bdring/FluidDial/data/jogbg.png

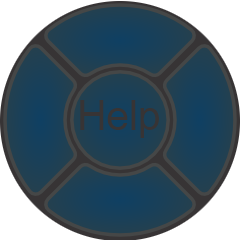
data/jogbg.png
