bdring/FluidDial/docs/images/switchConnectionScene.png

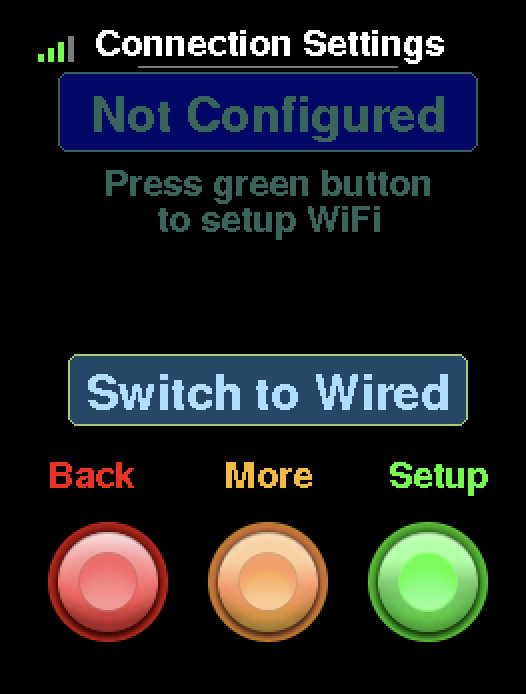
docs/images/switchConnectionScene.png
