bdring/FluidDial/src/Scene.cpp

// Copyright (c) 2023 Mitch Bradley
// Use of this source code is governed by a GPLv3 license that can be found in the LICENSE file.

#include "Scene.h"
#include "ConfigItem.h"
#include "System.h"
#ifdef USE_WIFI
#    include "WiFiConnection.h"
#endif

#ifndef ARDUINO
#    include <sys/stat.h>
#    include <sys/types.h>
#endif
#include <vector>

extern Scene homingScene;
extern Scene statusScene;

Scene* current_scene = nullptr;

int touchX;
int touchY;
int touchDeltaX;
int touchDeltaY;

std::vector<Scene*> scene_stack;

void activate_scene(Scene* scene, void* arg) {
    bool prev_show = !current_scene || current_scene->showButtons();
    if (current_scene) {
        current_scene->onExit();
    }
    current_scene = scene;
    current_scene->onEntry(arg);
    current_scene->reDisplay();
    if (current_scene->showButtons() != prev_show) {
        redrawButtons();
    }
}
void push_scene(Scene* scene, void* arg) {
    scene_stack.push_back(current_scene);
    activate_scene(scene, arg);
}
void pop_scene(void* arg) {
    if (scene_stack.size()) {
        Scene* last_scene = scene_stack.back();
        scene_stack.pop_back();
        activate_scene(last_scene, arg);
    }
}
void activate_at_top_level(Scene* scene, void* arg) {
    scene_stack.clear();
    activate_scene(scene, arg);
}
Scene* parent_scene() {
    return scene_stack.size() ? scene_stack.back() : nullptr;
}

bool touchIsCenter() {
    // Convert from screen coordinates to 0,0 in the center
    Point ctr = Point { touchX, touchY }.from_display();

    int center_radius = display_short_side() / 6;

    return (ctr.x * ctr.x + ctr.y * ctr.y) < (center_radius * center_radius);
}

void dispatch_button(bool pressed, int button) {
    switch (button) {
        case 0:
            if (pressed) {
                current_scene->onRedButtonPress();
            } else {
                current_scene->onRedButtonRelease();
            }
            break;
        case 1:
            if (pressed) {
                current_scene->onDialButtonPress();
            } else {
                current_scene->onDialButtonRelease();
            }
            break;
        case 2:
            if (pressed) {
                current_scene->onGreenButtonPress();
            } else {
                current_scene->onGreenButtonRelease();
            }
            break;
        default:
            break;
    }
}
void dispatch_touch() {
    static m5::touch_state_t last_touch_state = {};

    auto t = touch.getDetail();
    if (t.state != last_touch_state) {
        last_touch_state = t.state;
        touchX           = t.x - sprite_offset.x;
        touchY           = t.y - sprite_offset.y;
        int delta;
        if (screen_encoder(t.x, t.y, delta) && t.state == m5::touch_state_t::touch) {
            current_scene->onEncoder(delta);
            return;
        }
        int button;
       
        if (screen_button_touched(t.state == m5::touch_state_t::touch, t.x, t.y, button)) {
            if (t.state == m5::touch_state_t::touch) {
                dispatch_button(true, button);
            } else if (t.state == m5::touch_state_t::none) {
                dispatch_button(false, button);
            }
            return;
        }
        if (touchX < 0) {
            return;
        }
        if (t.state == m5::touch_state_t::touch) {
            current_scene->onTouchPress();
        } else if (t.state == m5::touch_state_t::none) {
            current_scene->onTouchRelease();
        }
        if (t.wasClicked()) {
            current_scene->onTouchClick();
        } else if (t.wasHold()) {
            current_scene->onTouchHold();
        } else if (t.state == m5::touch_state_t::flick_end) {
            touchDeltaX = t.distanceX();
            touchDeltaY = t.distanceY();

            int absX = abs(touchDeltaX);
            int absY = abs(touchDeltaY);
            if (absY > 60 && absX < (absY * 2)) {
                if (touchDeltaY > 0) {
                    current_scene->onDownFlick();
                } else {
                    current_scene->onUpFlick();
                }
            } else if (absX > 60 && absY < (absX * 2)) {
                if (touchDeltaX > 0) {
                    current_scene->onRightFlick();
                } else {
                    current_scene->onLeftFlick();
                }
            } else {
                current_scene->onTouchFlick();
            }
        }
    }
}

ActionHandler action = nullptr;

void schedule_action(ActionHandler _action) {
    action = _action;
}

// Coalesced redraw bookkeeping. See Scene.h for rationale.
static volatile bool s_redisplay_dirty   = false;
static uint32_t      s_last_redisplay_ms = 0;

void request_redisplay() {
    s_redisplay_dirty = true;
}

void service_redisplay() {
    if (!s_redisplay_dirty) {
        return;
    }
    uint32_t now = millis();
    // Cap UI refresh to UPDATE_RATE_MS (~30 ms). Multiple parser callbacks
    // in the same window collapse to one reDisplay.
    if ((int32_t)(now - s_last_redisplay_ms) < (int32_t)UPDATE_RATE_MS) {
        return;
    }
    s_redisplay_dirty   = false;
    s_last_redisplay_ms = now;
    if (current_scene) {
        current_scene->reDisplay();
    }
}

void dispatch_events() {
    update_events();
    service_config_requests();

    static int16_t oldEncoder   = 0;
    int16_t        newEncoder   = get_encoder();
    int16_t        encoderDelta = newEncoder - oldEncoder;
    if (encoderDelta) {
        oldEncoder = newEncoder;

        int16_t scaledDelta = current_scene->scale_encoder(encoderDelta);
        if (scaledDelta && !ui_locked()) {
            current_scene->onEncoder(scaledDelta);
        }
    }

    if (!ui_locked()) {
        bool pressed;
        int  button;
        if (switch_button_touched(pressed, button)) {
            dispatch_button(pressed, button);
        }

        dispatch_touch();
    }

    current_scene->onPoll();

    if (!fnc_is_connected()) {
        if (state != Disconnected) {
            set_disconnected_state();
#ifdef USE_WIFI
            wifi_force_ws_reconnect();
#endif
            extern Scene menuScene;
            activate_at_top_level(&menuScene);
            fnc_realtime(StatusReport);
        }
    }
    if (action) {
        action();
        action = nullptr;
    }
}

static const char* setting_name(const char* base_name, int axis) {
    static char name[32];
    if (axis == -1) {
        return base_name;
    }
    sprintf(name, "%s%c", base_name, axisNumToChar(axis));
    return name;
}

void Scene::setPref(const char* name, int value) {
    setPref(name, -1, value);
}
void Scene::getPref(const char* name, int* value) {
    getPref(name, -1, value);
}

void Scene::setPref(const char* base_name, int axis, int value) {
    if (!_prefs) {
        return;
    }
    nvs_set_i32(_prefs, setting_name(base_name, axis), value);
}
void Scene::getPref(const char* base_name, int axis, int* value) {
    if (!_prefs) {
        return;
    }
    nvs_get_i32(_prefs, setting_name(base_name, axis), reinterpret_cast<int32_t*>(value));
}
void Scene::setPref(const char* base_name, int axis, const char* value) {
    if (!_prefs) {
        return;
    }
    nvs_set_str(_prefs, setting_name(base_name, axis), value);
}
void Scene::getPref(const char* base_name, int axis, char* value, int maxlen) {
    if (!_prefs) {
        return;
    }
    size_t len = maxlen;
    nvs_get_str(_prefs, setting_name(base_name, axis), value, &len);
}
bool Scene::initPrefs() {
    if (_prefs) {
        return false;  // Already open
    }
    _prefs = nvs_init(name());
    return _prefs;
}

int Scene::scale_encoder(int delta) {
    _encoder_accum += delta;
    int res = _encoder_accum / _encoder_scale;
    _encoder_accum %= _encoder_scale;
    return res;
}

void Scene::background() {
    system_background();
}

void act_on_state_change() {
    current_scene->onStateChange(previous_state);
}
