bdring/FluidDial/src/SystemMacOS.cpp

// 2026 - Figamore
// Use of this source code is governed by a GPLv3 license that can be found in the LICENSE file.

// System interface routines for macOS (native SDL preview build)

#include "stdio.h"

#include "System.h"
#include "FluidNCModel.h"
#include "M5GFX.h"
#include "Drawing.h"
#include "NVS.h"
#ifdef USE_WIFI
#    include "WiFiConnection.h"
#    include "PeerLink.h"
#endif

#include <fcntl.h>
#include <termios.h>
#include <unistd.h>
#include <sys/stat.h>
#include <string.h>
#include <stdlib.h>

LGFX_Device& display = M5.Display;
LGFX_Sprite  canvas(&M5.Display);

m5::Speaker_Class& speaker = M5.Speaker;
m5::Touch_Class&   touch   = M5.Touch;

bool round_display = true;

void system_background() {
    drawPngFile("PCBackground.png", 0, 0);
}

void update_events() {
    lgfx::Panel_sdl::loop();
    M5.update();
}

extern "C" int milliseconds() {
    return m5gfx::millis();
}

void delay_ms(uint32_t ms) {
    SDL_Delay(ms);
}

void drawPngFile(const char* filename, int x, int y) {
    drawPngFile(&canvas, filename, x, y);
}
void drawPngFile(LGFX_Sprite* sprite, const char* filename, int x, int y) {
    std::string fn("data/");
    fn += filename;
    sprite->drawPngFile(fn.c_str(), x, -y, 0, 0, 0, 0, 1.0f, 1.0f, datum_t::middle_center);
}

static int serial_fd = -1;

static bool open_serial(const char* portname) {
    serial_fd = open(portname, O_RDWR | O_NOCTTY | O_NONBLOCK);
    if (serial_fd < 0) {
        printf("Can't open %s\n", portname);
        return false;
    }

    struct termios tty;
    tcgetattr(serial_fd, &tty);
    cfsetispeed(&tty, B115200);
    cfsetospeed(&tty, B115200);
    tty.c_cflag = (tty.c_cflag & ~CSIZE) | CS8;
    tty.c_cflag &= ~(PARENB | CSTOPB | CRTSCTS);
    tty.c_cflag |= CLOCAL | CREAD;
    tty.c_iflag  = IGNBRK | IGNPAR;
    tty.c_oflag  = 0;
    tty.c_lflag  = 0;
    tty.c_cc[VMIN]  = 0;
    tty.c_cc[VTIME] = 0;
    tcsetattr(serial_fd, TCSANOW, &tty);
    return true;
}

extern char* comname;

void init_system() {
    lgfx::Panel_sdl::setup();

    auto cfg = M5.config();
    M5.begin(cfg);

    if (comname != NULL) {
        if (!open_serial(comname)) {
            printf("Running without serial connection\n");
        }
    } else {
        printf("No serial port given — running in preview mode (no FluidNC connection)\n");
    }

    canvas.createSprite(display.width(), display.height());

    display.clear();
    speaker.setVolume(255);
}

Point sprite_offset { 0, 0 };

void show_logo() {}
void base_display() {
    display.clear();
}

int     num_layouts = 1;
int32_t layout_num  = 0;
void    next_layout(int delta) {}

void resetFlowControl() {}
void reinit_fnc_uart() {}

extern "C" void fnc_putchar(uint8_t c) {
    if (serial_fd >= 0) {
        write(serial_fd, &c, 1);
    }
}

extern "C" int fnc_getchar() {
    if (serial_fd < 0) {
        return -1;
    }
    char c;
    int  cnt = (int)read(serial_fd, &c, 1);
    if (cnt > 0) {
        update_rx_time();
        return (unsigned char)c;
    }
    return -1;
}

extern "C" void poll_extra() {}

extern "C" bool fnc_rx_waiting() { return false; }

void dbg_write(uint8_t c) {
    putchar(c);
}

void dbg_print(const char* s) {
    char c;
    while ((c = *s++) != '\0') {
        putchar(c);
    }
}

static bool outside_of_circle(int& x, int& y) {
    x -= display.width() / 2;
    y -= display.height() / 2;
    int magsq = x * x + y * y;
    return magsq > (120 * 120);
}

bool screen_encoder(int x, int y, int& delta) {
    if (!outside_of_circle(x, y)) {
        return false;
    }
    if (y >= 0) {
        return false;
    }

    int tangent = y * 100 / x;
    if (tangent < 0) {
        tangent = -tangent;
    }
    delta = 4;
    if (tangent > 172) {
        delta = 1;
    } else if (tangent > 100) {
        delta = 2;
    } else if (tangent > 58) {
        delta = 3;
    }
    if (x < 0) {
        delta = -delta;
    }
    return true;
}

bool screen_button_touched(bool pressed, int x, int y, int& button) {
    if (!outside_of_circle(x, y)) {
        return false;
    }
    if (x <= -90) {
        button = 0;
    } else if (x >= 90) {
        button = 2;
    } else {
        button = 1;
    }
    return true;
}

bool switch_button_touched(bool& pressed, int& button) {
    if (M5.BtnA.wasPressed()) {
        button  = 0;
        pressed = true;
        return true;
    }
    if (M5.BtnA.wasReleased()) {
        button  = 0;
        pressed = false;
        return true;
    }
    if (M5.BtnB.wasPressed()) {
        button  = 1;
        pressed = true;
        return true;
    }
    if (M5.BtnB.wasReleased()) {
        button  = 1;
        pressed = false;
        return true;
    }
    if (M5.BtnC.wasPressed()) {
        button  = 2;
        pressed = true;
        return true;
    }
    if (M5.BtnC.wasReleased()) {
        button  = 2;
        pressed = false;
        return true;
    }
    return false;
}

void ackBeep() {
    speaker.tone(1800, 50);
}

void deep_sleep(int us) {}

int16_t get_encoder() {
    return 0;
}

static FILE* prefFile(const char* handle, const char* pname, const char* mode) {
    static char fname[60];
    snprintf(fname, 60, "%s/%s", handle, pname);
    return fopen(fname, mode);
}

void nvs_get_str(nvs_handle_t handle, const char* name, char* value, size_t* len) {
    FILE* fd = prefFile(handle, name, "rb");
    if (fd) {
        *len = fread(value, 1, *len - 1, fd);
        fclose(fd);
    } else {
        *len = 0;
    }
    value[*len] = '\0';
}
void nvs_set_str(nvs_handle_t handle, const char* name, const char* value) {
    FILE* fd = prefFile(handle, name, "wb");
    if (fd) {
        fwrite(value, 1, strlen(value), fd);
        fclose(fd);
    }
}

void nvs_get_i32(nvs_handle_t handle, const char* name, int32_t* value) {
    char   strval[20];
    size_t len = 20;
    nvs_get_str(handle, name, strval, &len);
    if (*strval) {
        *value = atoi(strval);
    }
}
void nvs_set_i32(nvs_handle_t handle, const char* name, int32_t value) {
    char valstr[20];
    snprintf(valstr, 20, "%d", value);
    nvs_set_str(handle, name, valstr);
}

nvs_handle_t nvs_init(const char* name) {
    char dname[50];
    mkdir("prefs", 0755);
    snprintf(dname, 50, "prefs/%s", name);
    mkdir(dname, 0755);
    return strdup(dname);
}

bool ui_locked(bool redrawButtonsFlag) {
    return false;
}

void redrawButtons() {}

// -- Battery stubs for macOS preview builds (M5 Dial has no battery circuitry) --
int  battery_level()    { return -1; }
bool battery_charging() { return false; }

#ifdef USE_WIFI
// ── WiFi stubs for macOS preview builds ───────────────────────────────────────
// These let the WiFi scenes compile and render on the SDL simulator.
// All networking is no-op; status values are fixed to show a connected state.

static WiFiConfig _preview_cfg = { "Preview SSID", "", "192.168.1.100", false };

void        wifi_init(bool)               {}
void        wifi_poll()                    {}
bool        wifi_is_connected()            { return true; }
bool        websocket_is_connected()       { return true; }
void        wifi_force_ws_reconnect()      {}
void        wifi_shutdown()                {}
bool        wifi_in_ap_mode()              { return false; }
void        wifi_start_ap_setup()          {}
void        wifi_stop_ap_and_restart()     {}
void        wifi_stop_ap()                 {}
void        wifi_save_config(const char*, const char*, const char*) {}
WiFiConfig  wifi_load_config()             { return _preview_cfg; }
const char* wifi_ap_ssid()                 { return "FluidDial"; }
const char* wifi_status_str()              { return "Connected"; }
const bool  wifi_not_ready()               { return false; }
int         wifi_signal_bars()             { return 3; }
const char* wifi_last_error()              { return nullptr; }
WiFiConfig  wifi_active_config()           { return _preview_cfg; }
void        ws_putchar(uint8_t)            {}
int         ws_getchar()                   { return -1; }
bool          wifi_use_uart_mode()            { return false; }
void          wifi_set_uart_mode(bool)        {}
bool          wifi_is_first_boot()            { return false; }
TransportMode wifi_get_transport()            { return TransportMode::ESPNOW; }
void          wifi_set_transport(TransportMode) {}
bool          wifi_use_espnow_mode()          { return true; }
void          wifi_request_ota_reboot()       {}
bool          wifi_ota_boot_requested()       { return false; }

// ---- OTA stubs -----
// Default to the STA "ready" view. Define DEV_SIMULATED_OTA_AP to preview the
// AP-credentials view instead
void        wifi_start_ota_server()    {}
void        wifi_stop_ota_server()     {}
void        wifi_ota_force_ap_setup()  {}
int         wifi_ota_progress()        { return 0; }
const char* wifi_ota_ip()              { return "192.168.1.100"; }
const char* wifi_ota_error()           { return nullptr; }
#ifdef DEV_SIMULATED_OTA_AP
bool        wifi_ota_ap_mode()         { return true; }
bool        wifi_ota_sta_connected()   { return false; }
#else
bool        wifi_ota_ap_mode()         { return false; }
bool        wifi_ota_sta_connected()   { return true; }
#endif

// ESP-NOW stubs
void        espnow_init()                  {}
void        espnow_poll()                  {}
void        espnow_putchar(uint8_t)        {}
int         espnow_getchar()               { return -1; }
bool        espnow_is_paired()             { return true; }
bool        espnow_is_connected()          { return true; }
const char* espnow_status_str()            { return "Simulated"; }
void        espnow_start_pairing()         {}
void        espnow_cancel_pairing()        {}
bool        espnow_pairing_complete()      { return false; }
void        espnow_clear_pairing()         {}
bool        espnow_has_saved_pairing()     { return true; }
bool        espnow_is_reconnecting()       { return false; }
int8_t      espnow_rssi()                  { return 0; }
int         espnow_signal_bars()           { return 3; }
static constexpr size_t MOCK_ESPNOW_PROFILE_COUNT = 5;

size_t      espnow_profile_count()         { return MOCK_ESPNOW_PROFILE_COUNT; }
int         espnow_active_profile_index()  { return 0; }
bool        espnow_get_profile(size_t index, ESPNowProfileInfo& out) {
    memset(&out, 0, sizeof(out));
    if (index >= MOCK_ESPNOW_PROFILE_COUNT) return false;
    static const uint8_t macs[MOCK_ESPNOW_PROFILE_COUNT][6] = {
        {0x44, 0x1d, 0x64, 0xf2, 0x27, 0xe4},
        {0x24, 0x6f, 0x28, 0xaa, 0xbb, 0xcc},
        {0x94, 0xb9, 0x7e, 0x41, 0x94, 0x30},
        {0x30, 0xae, 0xa4, 0x18, 0x52, 0x71},
        {0x7c, 0xdf, 0xa1, 0x09, 0x63, 0xb8},
    };
    static const char* hostnames[MOCK_ESPNOW_PROFILE_COUNT] = {
        "shop-mill",
        "plotter",
        "laser-1",
        "plasma-cutter",
        "garage-cnc",
    };
    memcpy(out.mac, macs[index], sizeof(out.mac));
    out.channel = static_cast<uint8_t>(index + 1);
    out.active = index == 0;
    strlcpy(out.hostname, hostnames[index], sizeof(out.hostname));
    return true;
}
bool        espnow_select_profile(size_t)  { return true; }
bool        espnow_remove_profile(size_t)  { return true; }
#endif  // USE_WIFI
