bdring/FluidDial/src/MultiJogScene.cpp

// Copyright (c) 2023 Mitch Bradley
// Use of this source code is governed by a GPLv3 license that can be found in the LICENSE file.

#include "Config.h"

#include "Scene.h"
#include "ConfirmScene.h"
#include "e4math.h"
#include "System.h"  // dbg_printf()

//   Jog tracing — enable with -DJOG_TRACE
//   J s  send   t=<ms> a=<accum> dt=<ms since last send> f=<feed mm/min>
//               e=<estimated exec ms> o=<outstanding queue ms> b=<send block ms>
//   J rev        direction reversal -> JogCancel issued
//   J DROP       jog skipped because outstanding queue >= QUEUE_CAP_MS
//   J STOP       dial-still timeout -> jog cancelled
//   J P  send   precise-mode send (b=<send block ms>)
#ifdef JOG_TRACE
#    define JOG_DBG(...) dbg_printf(__VA_ARGS__)
#else
#    define JOG_DBG(...) ((void)0)
#endif

extern Scene helpScene;
extern Scene fileSelectScene;

static const char* jog_help_text[] = { "Jog Help",
                                       "Touch:",
                                       "Top/Bottom: choose axis",
                                       "Left/Right: set digit"
                                       "",
                                       "Turn: jog by digit",
                                       "Red/Grn: hold to jog",
                                       "Swipe left to exit",
                                       NULL };

bool jog_dynamic_mode();
void jog_toggle_mode();

// Jog settings / help screen (dial center)
// the green button toggles between the two jogging behaviors
#ifndef USE_M5
static const char* jog_help_lines[] = {
    "Top/Bottom: pick axis",
    "Left/Right: set digit",
    "Red/Grn: hold to jog",
    "Dial: zero   Swipe: exit",
    NULL,
};
#endif

class JogHelpScene : public Scene {
    void drawScreen() {
        drawBackground(BROWN);

        bool dyn = jog_dynamic_mode();
#ifdef USE_M5
        centered_text("Jog Mode", 48, WHITE, SMALL);
        centered_text(dyn ? "Dynamic" : "Precise", 84, dyn ? GREEN : YELLOW, MEDIUM);
        if (dyn) {
            centered_text("Follows the handwheel,", 120, WHITE, TINY);
            centered_text("stops when you stop.", 140, WHITE, TINY);
        } else {
            centered_text("Moves the exact number", 120, WHITE, TINY);
            centered_text("of clicks x step size.", 140, WHITE, TINY);
        }
        centered_text("Top/Bot: axis   L/R: digit", 170, WHITE, TINY);
#else
        centered_text("Jog Mode", 18, WHITE, SMALL);
        centered_text(dyn ? "Dynamic" : "Precise", 50, dyn ? GREEN : YELLOW, MEDIUM);
        if (dyn) {
            centered_text("Follows the handwheel,", 82, WHITE, TINY);
            centered_text("stops when you stop.", 102, WHITE, TINY);
        } else {
            centered_text("Moves the exact number", 82, WHITE, TINY);
            centered_text("of clicks x step size.", 102, WHITE, TINY);
        }
        int pos = 134;
        for (const char** p = jog_help_lines; *p; ++p) {
            centered_text(*p, pos, WHITE, TINY);
            pos += 20;
        }
#endif
        drawButtonLegends("", "Toggle", "Back");
        refreshDisplay();
    }

public:
    JogHelpScene() : Scene("Jog Mode") {}
    void onEntry(void* arg) override { drawScreen(); }
    void reDisplay() override { drawScreen(); }
    void onGreenButtonPress() override {
        jog_toggle_mode();
        drawScreen();
    }
    void onDialButtonPress() override { pop_scene(); }
    void onTouchClick() override {
        if (touchIsCenter()) {
            pop_scene();
        }
    }
} jogHelpScene;

class MultiJogScene : public Scene {
private:
    // Default to ones position for M5, and tenths position for CYD due to larger number of pulses generated by encoder handwheels
#ifdef USE_M5
    static const int DEFAULT_DIST_INDEX = 2;  // ones
#else
    static const int DEFAULT_DIST_INDEX = 1;  // tenths
#endif
    int          _dist_index[3] = { DEFAULT_DIST_INDEX, DEFAULT_DIST_INDEX, DEFAULT_DIST_INDEX };
    int          max_index() { return 6; }  // 10^3 = 1000;
    int          min_index() { return 0; }  // 10^3 = 1000;
    int          _selected_mask = 1 << 0;
    const int    num_axes       = 3;
    bool         _cancelling    = false;
    bool         _cancel_held   = false;
    bool         _continuous    = false;
    // Jog behavior: 1 = Dynamic (paced, handwheel-follow), 0 = Precise (exact
    // clicks x step size). Persists in NVS
    int          _dynamic_mode  = 1;
    // MPG jog rate-limiting: accumulate encoder ticks and send at most one
    // jog command per MPG_INTERVAL_MS to avoid flooding FluidNC's planner queue.
    static const uint32_t MPG_INTERVAL_MS = 30;   // min spacing between jog commands
    static const uint32_t MPG_STOP_MS     = 280;  // dial-still time that ends a jog
    static const uint32_t QUEUE_CAP_MS    = 180;  // max motion kept buffered ahead
    
    static const int      JOG_MAX_INFLIGHT = 3;

    static const uint32_t CANCEL_RESEND_MS = 80;
    static const uint32_t CANCEL_MIN_MS    = 250;
    static const uint32_t CANCEL_MAX_MS    = 1500;
    int      _mpg_accum        = 0;
    uint32_t _last_mpg_ms      = 0;
    uint32_t _last_mpg_tick_ms = 0;
    int8_t   _jog_dir          = 0;   // -1/0/+1: direction of the live dial jog
    uint32_t _jog_drain_ms     = 0;   // estimated millis() when the buffer empties
    bool     _mpg_jogging      = false;
    bool     _cancel_pending   = false;
    uint32_t _cancel_req_ms    = 0;
    uint32_t _last_cancel_ms   = 0;

public:
    MultiJogScene() : Scene("Jog", 4, jog_help_text) {}

    e4_t distance(int axis) { return e4_power10(_dist_index[axis] - num_digits()); }
    void unselect_all() { _selected_mask = 0; }
    bool selected(int axis) { return _selected_mask & (1 << axis); }
    bool only(int axis) { return _selected_mask == (1 << axis); }

    int  next(int axis) { return (axis < 2) ? axis + 1 : 0; }
    void select(int axis) { _selected_mask |= 1 << axis; }
    void unselect(int axis) { _selected_mask &= ~(1 << axis); }

    int the_selected_axis() {
        if ((_selected_mask & (_selected_mask - 1)) != 0) {
            return -2;  // Multiple axes are selected
        }
        for (size_t axis = 0; axis < num_axes; axis++) {
            if (selected(axis)) {
                return axis;
            }
        }
        return -1;  // No axis is selected
    }

    void drawJogBg() {
        // Recreate jogbg.png with drawing primitives — faster than rendering png which was causing heap issues with WiFi and overall sluggishness :(
        const int cx = 120, cy = 120;
        const int R  = 119;   // outer circle radius
        const int ri = 50;    // inner (center circle) radius
        const int hw = 3;     // half-width of separator bands (parallel edges)
        const uint16_t zone_color    = 0x1a4d;  // nicer blue
        const uint16_t sep_color     = 0x0000;  // black
        const uint16_t outline_color = 0x8410;

        // Fill entire outer disc with blue, then overlay separators + center
        canvas.fillCircle(cx, cy, R, zone_color);

        // Outer circle outline
        canvas.drawCircle(cx, cy, R, outline_color);

        // Wedges' inner radii outlines:
        canvas.drawCircle(cx, cy, ri + 1, outline_color);


        for (int sx = -1; sx <= 1; sx += 2) {
            for (int sy = -1; sy <= 1; sy += 2) {
                // along the diagonal
                int ax = (int)(sx * 0.72f * R);
                int ay = (int)(sy * 0.72f * R);
                // perpendicular offset for band width
                int px = (int)(-sy * 0.72f * hw);
                int py = (int)( sx * 0.72f * hw);
                // Rectangle corners: center±perp to edge±perp
                canvas.fillTriangle(cx + px, cy + py, cx - px, cy - py,
                                    cx + ax + px, cy + ay + py, sep_color);
                canvas.fillTriangle(cx - px, cy - py, cx + ax - px, cy + ay - py,
                                    cx + ax + px, cy + ay + py, sep_color);
                // Outline the separator edges
                int oax = (int)(sx * 0.71f * R);
                int oay = (int)(sy * 0.71f * R);
                int opx = (int)(-sy * 0.71f * hw);
                int opy = (int)( sx * 0.71f * hw);
                canvas.drawLine(cx + opx, cy + opy, cx + oax + opx, cy + oay + opy, outline_color);
                canvas.drawLine(cx - opx, cy - opy, cx + oax - opx, cy + oay - opy, outline_color);
            }
        }


        // Center circle void
        canvas.fillCircle(cx, cy, ri, sep_color);


        // Concentric circle
        canvas.fillCircle(cx, cy, ri - hw * 1.5, zone_color);

        // Inner circle outline
        canvas.drawCircle(cx, cy, ri - hw * 1.5, outline_color);

        // "Help" hint in center
        centered_text("Help", cy + 4, BLACK, MEDIUM);
    }

    void reDisplay() {
        background();
        drawJogBg();
        drawMenuTitle("Jog");
        if (state == Idle) {
            centered_text(_dynamic_mode ? "Dynamic" : "Precise", 45, 65535, SMALL);
        } else {
            drawStatus();
        }

        if (state != Jog && _cancelling) {
            _cancelling = false;
        }
        if (_cancelling || _cancel_held) {
            centered_text("Jog Canceled", 120, RED, MEDIUM);
        } else {
            DRO dro(16, 68, 210, 32);
            for (size_t axis = 0; axis < num_axes; axis++) {
                dro.draw(axis, _dist_index[axis], selected(axis));
            }
            if (state == Jog) {
                if (!_continuous) {
                    centered_text("Touch to cancel jog", 185, YELLOW, TINY);
                }
            } else {
                std::string dialLegend("Zero");
                for (int axis = 0; axis < num_axes; axis++) {
                    if (selected(axis)) {
                        dialLegend += axisNumToChar(axis);
                    }
                }
                drawButtonLegends("Jog-", "Jog+", dialLegend.c_str());
            }
        }
        refreshDisplay();
    }
    void zero_axes() {
        std::string cmd = "G10L20P0";
        for (int axis = 0; axis < num_axes; axis++) {
            if (selected(axis)) {
                cmd += axisNumToChar(axis);
                cmd += "0";
            }
        }
        send_line(cmd.c_str());
    }
    void onEntry(void* arg) {
        if (arg && strcmp((const char*)arg, "Confirmed") == 0) {
            zero_axes();
        }
        if (initPrefs()) {
            for (size_t axis = 0; axis < 3; axis++) {
                getPref("DistanceDigit", axis, &_dist_index[axis]);
            }
            getPref("JogMode", &_dynamic_mode);
        }
    }

    int which(int x, int y) {
        if (y > 130) {
            return 2;
        }
        return y > 90 ? 1 : 0;
    }

    void confirm_zero_axes() {
        std::string confirmMsg("Zero ");

        for (int axis = 0; axis < num_axes; axis++) {
            if (selected(axis)) {
                confirmMsg += axisNumToChar(axis);
            }
        }
        confirmMsg += " ?";
        dbg_println(confirmMsg.c_str());
        push_scene(&confirmScene, (void*)confirmMsg.c_str());
    }
    void set_dist_index(int axis, int value) {
        _dist_index[axis] = value;
        setPref("DistanceDigit", axis, value);
    }

    void increment_distance(int axis) {
        if (_dist_index[axis] < max_index()) {
            set_dist_index(axis, _dist_index[axis] + 1);
        }
    }
    void increment_distance() {
        for (int axis = 0; axis < num_axes; axis++) {
            if (selected(axis)) {
                increment_distance(axis);
            }
        }
    }
    void decrement_distance(int axis) {
        if (_dist_index[axis] > min_index()) {
            set_dist_index(axis, _dist_index[axis] - 1);
        }
    }

    void decrement_distance() {
        for (int axis = 0; axis < num_axes; axis++) {
            if (selected(axis)) {
                decrement_distance(axis);
            }
        }
    }
    void rotate_distance() {
        for (int axis = 0; axis < num_axes; axis++) {
            if (selected(axis)) {
                if (++_dist_index[axis] >= max_index()) {
                    _dist_index[axis] = min_index();
                }
            }
        }
    }
    void cancel_jog() {
        bool was_jogging = _continuous || _mpg_jogging || (state == Jog);
        _continuous       = false;
        _mpg_jogging      = false;
        _mpg_accum        = 0;
        _last_mpg_ms      = 0;
        _last_mpg_tick_ms = 0;
        _jog_dir          = 0;
        _jog_drain_ms     = 0;
        jog_reset_inflight();
        if (was_jogging) {
            fnc_realtime(JogCancel);
            _cancel_pending = true;
            _cancelling     = true;
            _cancel_req_ms  = millis();
            _last_cancel_ms = _cancel_req_ms;
        }
    }
    bool dynamicMode() { return _dynamic_mode; }
    void toggleMode() {
        cancel_jog();  // never leave motion running across a behavior change
        _dynamic_mode = !_dynamic_mode;
        setPref("JogMode", _dynamic_mode);
    }
    void next_axis() {
        int the_axis = the_selected_axis();
        if (the_axis == -2) {
            unselect_all();
            select(num_axes - 1);
            return;
        }
        if (the_axis == -1) {
            select(num_axes - 1);
            return;
        }
        unselect(the_axis);
        if (++the_axis == num_axes) {
            the_axis = 0;
        }
        select(the_axis);
    }
    void prev_axis() {
        int the_axis = the_selected_axis();
        if (the_axis == -2) {
            unselect_all();
            select(0);
            return;
        }
        if (the_axis == -1) {
            select(0);
            return;
        }
        unselect(the_axis);
        if (--the_axis < 0) {
            the_axis = num_axes - 1;
        }
        select(the_axis);
    }
    void touch_top() {
        prev_axis();
        reDisplay();
    }
    void touch_bottom() {
        next_axis();
        reDisplay();
    }
    void touch_left() {
        increment_distance();
        reDisplay();
    }
    void touch_right() {
        decrement_distance();
        reDisplay();
    }

    void onTouchPress() {
        if (state == Jog) {
            _cancel_held = true;
            cancel_jog();
        }
        reDisplay();
    }

    void onTouchRelease() {
        _cancel_held = false;
        reDisplay();
    }

    void onTouchClick() {
        if (state == Jog || _cancelling || _cancel_held) {
            return;
        }
        if (touchIsCenter()) {
            push_scene(&jogHelpScene);
            return;
        }

        // Convert from screen coordinates to 0,0 in the center
        Point ctr = Point { touchX, touchY }.from_display();

        int x = ctr.x;
        int y = ctr.y;

        int center_radius = display_short_side() / 6;

        // Sense touches at top, bottom, left, and right
        if (std::abs(y) > std::abs(x)) {
            if (y > 0) {
                touch_top();
            } else {
                touch_bottom();
            }
        } else {
            if (x > 0) {
                touch_right();
            } else {
                touch_left();
            }
        }
    }
    void onTouchHold() {
        // Select multiple axes
        if (touchX < 80) {
            int axis = which(touchX, touchY);
            if (selected(axis) && !only(axis)) {
                unselect(axis);
            } else {
                select(axis);
            }
            reDisplay();
            return;
        }
#if 0
        if (touchX < 160 && touchY > 160) {
            confirm_zero_axes();
        }
#endif
    }

    void onRightFlick() override {
        activate_scene(&fileSelectScene);
    }

    void onDialButtonPress() {
        zero_axes();
    }

    e4_t mpg_move_distance(int delta) {
        e4_t move = 0;
        for (int axis = 0; axis < num_axes; ++axis) {
            if (selected(axis)) {
                move = e4_magnitude(move, delta * distance(axis));
            }
        }
        return move;
    }

    void send_mpg_jog(int delta, e4_t feed) {
        std::string cmd("$J=G91");
        cmd += inInches ? "G20" : "G21";
        cmd += "F";
        cmd += e4_to_cstr(feed, 0);
        for (int axis = 0; axis < num_axes; ++axis) {
            if (selected(axis)) {
                cmd += axisNumToChar(axis);
                cmd += e4_to_cstr(delta * distance(axis), inInches ? 3 : 2);
            }
        }
        send_jog_line(cmd.c_str());
        _mpg_jogging = true;
    }
    void start_button_jog(bool negative) {
        // e.g. $J=G91F1000X-10000
        e4_t total_distance = 0;
        int  n_axes         = 0;
        for (int axis = 0; axis < num_axes; ++axis) {
            if (selected(axis)) {
                total_distance = e4_magnitude(total_distance, distance(axis));
                ++n_axes;
            }
        }

        e4_t feedrate = total_distance * 300;  // go 5x the highlighted distance in 1 second

        std::string cmd("$J=G91");
        cmd += inInches ? "G20" : "G21";
        cmd += "F";
        cmd += e4_to_cstr(feedrate, 3);
        for (int axis = 0; axis < num_axes; ++axis) {
            if (selected(axis)) {
                e4_t axis_distance;
                if (n_axes == 1) {
                    axis_distance = e4_from_int(inInches ? 200 : 5000);
                } else {
                    axis_distance = distance(axis) * 20;
                }
                if (negative) {
                    axis_distance = -axis_distance;
                }
                cmd += axisNumToChar(axis);
                cmd += e4_to_cstr(axis_distance, 0);
            }
        }
        send_jog_line(cmd.c_str());
        _continuous = true;
    }

    void onGreenButtonPress() {
        if (state == Idle) {
            start_button_jog(false);
        }
    }
    void onGreenButtonRelease() {
        cancel_jog();
    }
    void onRedButtonPress() {
        if (state == Idle) {
            start_button_jog(true);
        }
    }
    void onRedButtonRelease() {
        cancel_jog();
    }

    void service_mpg(bool force = false) {
        if (_mpg_accum == 0) {
            return;
        }
        uint32_t now = millis();
        if (!force && (now - _last_mpg_ms) < MPG_INTERVAL_MS) {
            return;
        }

        int dir = (_mpg_accum > 0) ? 1 : -1;

        if (_jog_dir != 0 && dir != _jog_dir) {
            JOG_DBG("J rev t=%u %d->%d\n", (unsigned)now, _jog_dir, dir);
            fnc_realtime(JogCancel);
            jog_reset_inflight();
            _jog_drain_ms = now;
        }

        if (!force && jog_inflight() >= JOG_MAX_INFLIGHT) {
            JOG_DBG("J WAIT t=%u a=%d if=%d\n", (unsigned)now, _mpg_accum, jog_inflight());
            return;
        }

        _cancel_pending = false;
        _cancelling     = false;

        e4_t move = mpg_move_distance(_mpg_accum);
        if (move == 0) {
            _mpg_accum   = 0;
            _last_mpg_ms = now;
            return;
        }

        // Velocity-matched feed: feed[units/min] = move / dt * 60000ms
        uint32_t dt     = (_last_mpg_ms == 0) ? MPG_INTERVAL_MS : (now - _last_mpg_ms);
        int64_t  feed64 = (int64_t)move * 60000 / (int64_t)dt;
        e4_t     f_max  = e4_from_int(inInches ? 400 : 10000);
        e4_t     f_min  = e4_from_int(inInches ? 40 : 1000);
        e4_t     feed   = (feed64 > f_max) ? f_max : (feed64 < f_min ? f_min : (e4_t)feed64);

        uint32_t outstanding = (_jog_drain_ms > now) ? (_jog_drain_ms - now) : 0;
        if (!force && outstanding >= QUEUE_CAP_MS) {
            JOG_DBG("J DROP t=%u a=%d o=%u\n", (unsigned)now, _mpg_accum, (unsigned)outstanding);
            _mpg_accum   = 0;
            _last_mpg_ms = now;
            return;
        }

        int      acc = _mpg_accum;  // captured for trace
        uint32_t t0  = millis();
        send_mpg_jog(_mpg_accum, feed);
        jog_mark_sent();
        uint32_t blk = millis() - t0;  // time spent ack-gated waiting for the prior "ok"
        _jog_dir = dir;

        // Track the estimated buffer drain time
        uint32_t exec_ms = (uint32_t)((int64_t)move * 60000 / feed);
        uint32_t base    = (_jog_drain_ms > now) ? _jog_drain_ms : now;
        _jog_drain_ms    = base + exec_ms;

        JOG_DBG("J s t=%u a=%d dt=%u f=%ld e=%u o=%u b=%u\n",
                (unsigned)now, acc, (unsigned)dt, (long)(feed / 10000),
                (unsigned)exec_ms, (unsigned)outstanding, (unsigned)blk);

        _mpg_accum   = 0;
        _last_mpg_ms = now;
    }

    // Precise mode: move by exactly (detents x step size). Each finite $J
    // completes on its own, so the final position always equals the dialed-in count
    void precise_flush() {
        if (_mpg_accum == 0) {
            return;
        }
        uint32_t now = millis();
        if ((now - _last_mpg_ms) >= MPG_INTERVAL_MS) {
            if (jog_inflight() >= JOG_MAX_INFLIGHT) {
                JOG_DBG("J WAIT t=%u a=%d if=%d\n", (unsigned)now, _mpg_accum, jog_inflight());
                return;
            }
            _cancel_pending = false;
            _cancelling     = false;
            int      acc = _mpg_accum;
            uint32_t t0  = millis();
            send_mpg_jog(_mpg_accum, e4_from_int(inInches ? 400 : 10000));
            jog_mark_sent();
            JOG_DBG("J P t=%u a=%d b=%u\n", (unsigned)now, acc, (unsigned)(millis() - t0));
            _mpg_accum   = 0;
            _last_mpg_ms = now;
        }
    }

    // Tenths and hundreths unit steps jog more smoothly in precise mode and update fast enough to feel real-time
    bool dynamic_jog_active() {
        if (!_dynamic_mode) {
            return false;
        }
        for (int axis = 0; axis < num_axes; axis++) {
            if (selected(axis) && _dist_index[axis] >= num_digits()) {
                return true;
            }
        }
        return false;
    }

    void onEncoder(int delta) {
        _mpg_accum += delta;
        _last_mpg_tick_ms = millis();
        if (dynamic_jog_active()) {
            service_mpg();
        } else {
            precise_flush();
        }
    }

    void onPoll() override {
        if (dynamic_jog_active()) {
            service_mpg();
            // Stop jogging once the dial has been still long enough
            if (_mpg_jogging && _last_mpg_tick_ms != 0) {
                uint32_t now = millis();
                if ((now - _last_mpg_tick_ms) >= MPG_STOP_MS) {
                    service_mpg(true);
                    if (_mpg_accum == 0) {
                        JOG_DBG("J STOP t=%u\n", (unsigned)now);
                        cancel_jog();
                    }
                }
            }
        } else {
            precise_flush();
        }
        // Resend the cancel until the controller confirms it has left the Jog state
        if (_cancel_pending) {
            uint32_t now   = millis();
            uint32_t since = now - _cancel_req_ms;
            if ((state != Jog && since >= CANCEL_MIN_MS) || since >= CANCEL_MAX_MS) {
                _cancel_pending = false;
            } else if ((now - _last_cancel_ms) >= CANCEL_RESEND_MS) {
                fnc_realtime(JogCancel);
                _last_cancel_ms = now;
            }
        }
    }

    void onDROChange() {
        reDisplay();
    }
    void onLimitsChange() {
        reDisplay();
    }
    void onAlarm() {
        reDisplay();
    }
    void onExit() {
        cancel_jog();
    }
} multiJogScene;

bool jog_dynamic_mode() { return multiJogScene.dynamicMode(); }
void jog_toggle_mode() { multiJogScene.toggleMode(); }
