bdring/FluidDial/src/ESPNowCrypto.cpp

// 2026 - Figamore

#ifdef ARDUINO
#ifdef USE_WIFI
#ifdef USE_ESPNOW

#include "ESPNowCrypto.h"

#include <esp_random.h>
#include <mbedtls/ecdh.h>
#include <mbedtls/ecp.h>
#include <mbedtls/md.h>
#include <mbedtls/sha256.h>
#include <string.h>

namespace {

constexpr uint32_t kReplayRegenMs = 3000;
constexpr uint32_t kReplayUnderflowLimit = 8;
constexpr char kPairingWindowLabel[] = "fluidnc-espnow-pairing-window-v1";
constexpr char kPairingSessionLabel[] = "fluidnc-espnow-pairing-session-v1";
constexpr char kEspNowPmkLabel[] = "fluiddial-espnow-pmk-v1";

int ecdhRng(void*, unsigned char* output, size_t len) {
    for (size_t i = 0; i < len; i += sizeof(uint32_t)) {
        uint32_t word = esp_random();
        size_t chunk = (len - i < sizeof(word)) ? (len - i) : sizeof(word);
        memcpy(output + i, &word, chunk);
    }
    return 0;
}

}  // namespace

namespace ESPNowCrypto {

void derivePairingWindowLmk(uint8_t out_lmk[16]) {
    uint8_t hash[32];
    mbedtls_sha256(reinterpret_cast<const uint8_t*>(kPairingWindowLabel), strlen(kPairingWindowLabel), hash, 0);
    memcpy(out_lmk, hash, 16);
    secureZero(hash, sizeof(hash));
}

void derivePmk(uint8_t out_pmk[16]) {
    uint8_t hash[32];
    mbedtls_sha256(reinterpret_cast<const uint8_t*>(kEspNowPmkLabel), strlen(kEspNowPmkLabel), hash, 0);
    memcpy(out_pmk, hash, 16);
}

void pairingAuthTag(const uint8_t key[16], const uint8_t* data, size_t len, uint8_t out[16]) {
    uint8_t full[32];
    mbedtls_md_context_t ctx;
    const mbedtls_md_info_t* info = mbedtls_md_info_from_type(MBEDTLS_MD_SHA256);

    mbedtls_md_init(&ctx);
    mbedtls_md_setup(&ctx, info, 1);
    mbedtls_md_hmac_starts(&ctx, key, 16);
    mbedtls_md_hmac_update(&ctx, data, len);
    mbedtls_md_hmac_finish(&ctx, full);
    mbedtls_md_free(&ctx);

    memcpy(out, full, 16);
}

bool verifyPairingAuthTag(const uint8_t key[16], const uint8_t* data, size_t len, const uint8_t tag[16]) {
    uint8_t expected[16];
    pairingAuthTag(key, data, len, expected);
    bool ok = constantTimeEquals(expected, tag, 16);
    secureZero(expected, sizeof(expected));
    return ok;
}

bool generateEcdhKeypair(uint8_t private_key[ECDH_PRIVATE_KEY_SIZE], uint8_t public_key[ECDH_PUBLIC_KEY_SIZE]) {
    mbedtls_ecp_group group;
    mbedtls_mpi d;
    mbedtls_ecp_point q;
    size_t olen = 0;
    bool ok = false;

    mbedtls_ecp_group_init(&group);
    mbedtls_mpi_init(&d);
    mbedtls_ecp_point_init(&q);

    if (mbedtls_ecp_group_load(&group, MBEDTLS_ECP_DP_SECP256R1) == 0 &&
        mbedtls_ecp_gen_keypair(&group, &d, &q, ecdhRng, nullptr) == 0 &&
        mbedtls_mpi_write_binary(&d, private_key, ECDH_PRIVATE_KEY_SIZE) == 0 &&
        mbedtls_ecp_point_write_binary(&group,
                                       &q,
                                       MBEDTLS_ECP_PF_UNCOMPRESSED,
                                       &olen,
                                       public_key,
                                       ECDH_PUBLIC_KEY_SIZE) == 0 &&
        olen == ECDH_PUBLIC_KEY_SIZE) {
        ok = true;
    }

    mbedtls_ecp_point_free(&q);
    mbedtls_mpi_free(&d);
    mbedtls_ecp_group_free(&group);
    if (!ok) {
        secureZero(private_key, ECDH_PRIVATE_KEY_SIZE);
        secureZero(public_key, ECDH_PUBLIC_KEY_SIZE);
    }
    return ok;
}

bool deriveEcdhSharedSecret(const uint8_t private_key[ECDH_PRIVATE_KEY_SIZE],
                            const uint8_t peer_public_key[ECDH_PUBLIC_KEY_SIZE],
                            uint8_t shared_secret[ECDH_SHARED_SECRET_SIZE]) {
    mbedtls_ecp_group group;
    mbedtls_mpi d;
    mbedtls_mpi z;
    mbedtls_ecp_point q;
    bool ok = false;

    mbedtls_ecp_group_init(&group);
    mbedtls_mpi_init(&d);
    mbedtls_mpi_init(&z);
    mbedtls_ecp_point_init(&q);

    if (mbedtls_ecp_group_load(&group, MBEDTLS_ECP_DP_SECP256R1) == 0 &&
        mbedtls_mpi_read_binary(&d, private_key, ECDH_PRIVATE_KEY_SIZE) == 0 &&
        mbedtls_ecp_point_read_binary(&group, &q, peer_public_key, ECDH_PUBLIC_KEY_SIZE) == 0 &&
        mbedtls_ecp_check_pubkey(&group, &q) == 0 &&
        mbedtls_ecdh_compute_shared(&group, &z, &q, &d, ecdhRng, nullptr) == 0 &&
        mbedtls_mpi_write_binary(&z, shared_secret, ECDH_SHARED_SECRET_SIZE) == 0) {
        ok = true;
    }

    mbedtls_ecp_point_free(&q);
    mbedtls_mpi_free(&z);
    mbedtls_mpi_free(&d);
    mbedtls_ecp_group_free(&group);
    if (!ok) {
        secureZero(shared_secret, ECDH_SHARED_SECRET_SIZE);
    }
    return ok;
}

void derivePairingSessionLmk(const uint8_t pairing_window_lmk[16],
                             const uint8_t shared_secret[ECDH_SHARED_SECRET_SIZE],
                             const uint8_t* discovery,
                             size_t discovery_len,
                             const uint8_t* challenge,
                             size_t challenge_len,
                             uint8_t out_lmk[16]) {
    uint8_t full[32];
    mbedtls_md_context_t ctx;
    const mbedtls_md_info_t* info = mbedtls_md_info_from_type(MBEDTLS_MD_SHA256);

    mbedtls_md_init(&ctx);
    mbedtls_md_setup(&ctx, info, 1);
    mbedtls_md_hmac_starts(&ctx, pairing_window_lmk, 16);
    mbedtls_md_hmac_update(&ctx, reinterpret_cast<const uint8_t*>(kPairingSessionLabel), strlen(kPairingSessionLabel));
    mbedtls_md_hmac_update(&ctx, shared_secret, ECDH_SHARED_SECRET_SIZE);
    mbedtls_md_hmac_update(&ctx, discovery, discovery_len);
    mbedtls_md_hmac_update(&ctx, challenge, challenge_len);
    mbedtls_md_hmac_finish(&ctx, full);
    mbedtls_md_free(&ctx);

    memcpy(out_lmk, full, 16);
    secureZero(full, sizeof(full));
}

bool constantTimeEquals(const uint8_t* a, const uint8_t* b, size_t len) {
    if (!a || !b) {
        return false;
    }
    uint8_t diff = 0;
    for (size_t i = 0; i < len; ++i) {
        diff |= (uint8_t)(a[i] ^ b[i]);
    }
    return diff == 0;
}

void secureZero(void* data, size_t len) {
    if (!data) {
        return;
    }
    volatile uint8_t* p = reinterpret_cast<volatile uint8_t*>(data);
    while (len--) {
        *p++ = 0;
    }
}

uint32_t randomNonce() {
    uint32_t nonce;
    do {
        nonce = esp_random();
    } while (nonce == 0);
    return nonce;
}

void issueRxChallenge(std::atomic<uint32_t>& rx_nonce) {
    rx_nonce.store(randomNonce(), std::memory_order_release);
}

bool stampAntiReplayTag(std::atomic<bool>& tx_peer_known,
                        std::atomic<uint32_t>& tx_peer_nonce,
                        std::atomic<uint32_t>& tx_counter,
                        uint8_t tag[8]) {
    if (!tx_peer_known.load(std::memory_order_acquire)) {
        return false;
    }
    uint32_t nonce = tx_peer_nonce.load(std::memory_order_acquire);
    uint32_t counter = tx_counter.fetch_add(1, std::memory_order_relaxed) + 1;
    memcpy(tag, &nonce, 4);
    memcpy(tag + 4, &counter, 4);
    return true;
}

bool acceptReplay(std::atomic<uint32_t>& rx_nonce,
                  ReplayState& replay,
                  uint32_t nonce,
                  uint32_t counter,
                  uint32_t now_ms) {
    uint32_t current = rx_nonce.load(std::memory_order_acquire);
    if (current != replay.win_nonce) {
        replay.win_nonce = current;
        replay.win_top = 0;
        replay.win_bitmap = 0;
        replay.underflow = 0;
    }
    if (nonce != current || counter == 0) {
        return false;
    }

    if (counter > replay.win_top) {
        uint32_t shift = counter - replay.win_top;
        replay.win_bitmap = (shift >= 64) ? 0ULL : (replay.win_bitmap << shift);
        replay.win_bitmap |= 1ULL;
        replay.win_top = counter;
        replay.underflow = 0;
        return true;
    }

    uint32_t diff = replay.win_top - counter;
    if (diff < 64) {
        uint64_t mask = 1ULL << diff;
        if (replay.win_bitmap & mask) {
            return false;
        }
        replay.win_bitmap |= mask;
        return true;
    }

    if (++replay.underflow >= kReplayUnderflowLimit) {
        if ((uint32_t)(now_ms - replay.regen_ms) > kReplayRegenMs) {
            replay.regen_ms = now_ms;
            issueRxChallenge(rx_nonce);
        }
        replay.underflow = 0;
    }
    return false;
}

}  // namespace ESPNowCrypto

#endif
#endif
#endif
