bdring/FluidDial/src/Touch_Class.cpp

// Copyright (c) M5Stack. All rights reserved.
// Licensed under the MIT license. See LICENSE file in the project root for full license information.

#include "Touch_Class.hpp"

namespace m5 {
    void Touch_Class::update(std::uint32_t msec) {
        if (msec - _last_msec <= TOUCH_MIN_UPDATE_MSEC)  /// Avoid high frequency updates
        {
            if (_detail_count == 0) {
                return;
            }
            std::size_t count = 0;
            for (std::size_t i = 0; i < TOUCH_MAX_POINTS; ++i) {
                count += update_detail(&_touch_detail[i], msec);
            }
            _detail_count = count;
            return;
        }

        _last_msec        = msec;
        std::size_t count = _gfx->getTouchRaw(_touch_raw, TOUCH_MAX_POINTS);
        if (!(count || _detail_count)) {
            return;
        }

        uint32_t updated_id = 0;
        if (count) {
            lgfx::touch_point_t tp[TOUCH_MAX_POINTS];
            memcpy(tp, _touch_raw, sizeof(lgfx::touch_point_t) * count);
            _gfx->convertRawXY(tp, count);
            for (std::size_t i = 0; i < count; ++i) {
                if (tp[i].id < TOUCH_MAX_POINTS) {
                    updated_id |= 1 << tp[i].id;
                    update_detail(&_touch_detail[tp[i].id], msec, true, &tp[i]);
                }
            }
        }
        {
            for (std::size_t i = 0; i < TOUCH_MAX_POINTS; ++i) {
                if ((!(updated_id & (1 << i))) && update_detail(&_touch_detail[i], msec, false, nullptr) && (count < TOUCH_MAX_POINTS)) {
                    ++count;
                }
            }
        }
        _detail_count = count;
    }

    bool Touch_Class::update_detail(touch_detail_t* det, std::uint32_t msec, bool pressed, lgfx::touch_point_t* tp) {
        touch_state_t tm = det->state;
        if (tm == touch_state_t::none && !pressed) {
            return false;
        }
        tm = static_cast<touch_state_t>(tm & ~touch_state_t::mask_change);
        if (pressed) {
            det->prev_x = det->x;
            det->prev_y = det->y;
            det->size   = tp->size;
            det->id     = tp->id;
            if (!(tm & touch_state_t::mask_moving)) {  // Processing when not flicked.
                if (tm & touch_state_t::mask_touch) {  // Not immediately after the touch.
                    if (abs(det->base_x - tp->x) > _flickThresh || abs(det->base_y - tp->y) > _flickThresh) {
                        det->prev = det->base;
                        tm        = static_cast<touch_state_t>(tm | touch_state_t::flick_begin);
                    } else if ((tm == touch) && (msec - det->base_msec > _msecHold)) {
                        tm = touch_state_t::hold_begin;
                    }
                } else {
                    *(static_cast<lgfx::touch_point_t*>(det)) = *tp;
                    tm                                        = touch_state_t::touch_begin;
                    det->base_msec                            = msec;
                    det->base_x                               = tp->x;
                    det->base_y                               = tp->y;
                    det->prev                                 = det->base;
                }
            }
            if (tm & mask_moving) {
                det->x = tp->x;
                det->y = tp->y;
            }
        } else {
            tm = (tm & touch_state_t::mask_touch) ?
                     static_cast<touch_state_t>((tm | touch_state_t::mask_change) & ~touch_state_t::mask_touch) :
                     touch_state_t::none;
        }
        det->state = tm;
        return true;
    }

    bool Touch_Class::update_detail(touch_detail_t* det, std::uint32_t msec) {
        touch_state_t tm = det->state;
        if (tm == touch_state_t::none) {
            return false;
        }
        tm = static_cast<touch_state_t>(tm & ~touch_state_t::mask_change);
        if (tm & touch) {
            det->prev_x = det->x;
            det->prev_y = det->y;
            if ((tm == touch) && (msec - det->base_msec > _msecHold)) {
                tm = touch_state_t::hold_begin;
            }
        } else {
            tm = touch_state_t::none;
        }
        det->state = tm;
        return true;
    }
}
