bdring/FluidDial/src/FluidNCModel.h

// Copyright (c) 2023 Mitch Bradley
// Use of this source code is governed by a GPLv3 license that can be found in the LICENSE file.

#pragma once
#include "GrblParserC.h"

// Same states as FluidNC except for the last one
enum state_t {
    Idle = 0,   // Must be zero.
    Alarm,      // In alarm state. Locks out all g-code processes. Allows settings access.
    CheckMode,  // G-code check mode. Locks out planner and motion only.
    Homing,     // Performing homing cycle
    Cycle,      // Cycle is running or motions are being executed.
    Hold,       // Active feed hold
    Jog,        // Jogging mode.
    DoorOpen,
    DoorClosed,
    GrblSleep,     // Sleep state.
    ConfigAlarm,   // You can't do anything but fix your config file.
    Critical,      // You can't do anything but reset with CTRL-x or the reset button
    Disconnected,  // We can't talk to FluidNC
};

// Variables and functions to model the state of the FluidNC controller

extern state_t     state;
extern state_t     previous_state;
extern const char* my_state_string;

extern int                n_axes;
extern pos_t              myAxes[6];
extern bool               myLimitSwitches[6];
extern bool               myProbeSwitch;
extern const char*        myCtrlPins;
extern const char*        myFile;
extern file_percent_t     myPercent;
extern override_percent_t myFro;
extern override_percent_t mySro;
extern uint32_t           myFeed;
extern uint32_t           mySpeed;
extern int                lastAlarm;
extern int                lastError;
extern uint32_t           errorExpire;
extern bool               inInches;
extern uint32_t           mySelectedTool;

int num_digits();

void send_line(const char* s, int timeout = 2000);
void send_jog_line(const char* s);  // jog send without the "ok" handshake
void send_linef(const char* fmt, ...);

void jog_mark_sent();       // record that a jog line was just streamed
int  jog_inflight();        // jogs sent but not yet acked (self-heals if stalled)
void jog_reset_inflight();  // clear (on JogCancel / jog stop)

const char* intToCStr(int val);
const char* axisNumToCStr(int axis);
char        axisNumToChar(int axis);

state_t     decode_state_string(const char* state_string);
const char* decode_error_number(int error_num);
const char* mode_string();

bool fnc_is_connected();
void set_disconnected_state();

void update_rx_time();

// Bounded boot-time probe over UART: discards bootloader noise then sends
// XON + status-report queries until FluidNC responds, or `budget_ms`
// elapses. Returns true on response. Bytes read here are discarded, NOT
// fed to the parser — current_scene may not be set yet at boot time.
bool pendant_wait_for_fluidnc_ready(uint32_t budget_ms);

extern pos_t toMm(pos_t position);
extern pos_t fromMm(pos_t position);
