bdring/FluidDial/src/DisplaySettingsScene.h

#pragma once

#ifdef USE_WIFI

#include "Scene.h"

class DisplaySettingsScene : public Scene {
public:
    DisplaySettingsScene() : Scene("Display", 4) {}

    void onEntry(void* arg = nullptr) override;
    void onEncoder(int delta) override;
    void onDialButtonPress() override;
    void onRedButtonPress() override;
    void onGreenButtonPress() override;
    void reDisplay() override;
};

extern DisplaySettingsScene displaySettingsScene;

#endif  // USE_WIFI
