bdring/FluidDial/src/Text.h

// Copyright (c) 2023 Mitch Bradley
// Use of this source code is governed by a GPLv3 license that can be found in the LICENSE file.

// Simplified ways to display text, hiding details of the graphics layer

#pragma once
#include "System.h"
#include "Point.h"

enum fontnum_t {
    TINY        = 0,
    SMALL       = 1,
    MEDIUM      = 2,
    LARGE       = 3,
    MEDIUM_MONO = 4,
};

// adjusts text to fit in (w) display area. reduces font size until it. tryfonts::false just uses fontnum
void auto_text(const std::string& txt,
               int                x,
               int                y,
               int                w,
               int                color,
               fontnum_t          fontnum  = MEDIUM,
               int                datum    = middle_center,
               bool               tryfonts = true,
               bool               trimleft = false);

void auto_text(const std::string& txt,
               Point              xy,
               int                w,
               int                color,
               fontnum_t          fontnum  = MEDIUM,
               int                datum    = middle_center,
               bool               tryfonts = true,
               bool               trimleft = false);

void text(const char* msg, int x, int y, int color, fontnum_t fontnum = TINY, int datum = middle_center);
void text(const std::string& msg, int x, int y, int color, fontnum_t fontnum = TINY, int datum = middle_center);

void text(const char* msg, Point xy, int color, fontnum_t fontnum = TINY, int datum = middle_center);
void text(const std::string& msg, Point xy, int color, fontnum_t fontnum = TINY, int datum = middle_center);

void centered_text(const char* msg, int y, int color = WHITE, fontnum_t fontnum = TINY);
void wrapped_text(const char* msg, int y, int w, int color = WHITE, fontnum_t fontnum = TINY);
